toragee/EQToolTouch/EQTool/Battery.h

/*****************************************************************************
 *  Battery.h  -  ESP32-C6-Touch-LCD-1.47 배터리 전압 읽기
 *
 *  회로도 (BAT 블록):
 *      VBAT --[ R21 200K ]--+--[ R22 100K ]-- GND
 *                           |
 *                        BAT_ADC (GPIO0)
 *
 *  분압비 = (200K + 100K) / 100K = 3
 *  => VBAT = ADC 읽은 전압 x 3
 *
 *  1셀 LiPo 만충 4.2V -> ADC 에는 1.4V 가 걸리므로 C6 ADC 범위에 여유가 있다.
 *
 *  ※ USB 가 꽂혀 있으면 충전 IC(ETA6098)가 전압을 끌어올리기 때문에
 *    이 값은 "배터리 잔량" 이 아니라 "충전 전압" 이다. 잔량으로 쓰지 말 것.
 ****************************************************************************/
#pragma once

#include <Arduino.h>

#define BAT_ADC_PIN     0           /* 회로도 BAT_ADC */
#define BAT_DIV_RATIO   3.0f        /* (200K + 100K) / 100K */
#define BAT_OVERSAMPLE  16          /* 평균 횟수 (노이즈 억제) */

/*  실측 보정 계수.
 *  분압 저항 오차(±1% 급 두 개)와 ESP32-C6 ADC 캘리브레이션(±2~3%)이
 *  겹치면 몇 %씩 어긋난다. 보통 낮게 읽힌다.
 *
 *  구하는 법: USB 를 꽂아 만충시킨 뒤
 *      1) 멀티미터로 배터리 단자 전압을 잰다        (예: 4.21 V)
 *      2) 같은 시점의 [BAT] 로그 값을 본다           (예: 4012 mV)
 *      3) BAT_CAL = 실측 / 로그 = 4210 / 4012 = 1.049
 *
 *  1.0 이면 보정 없음. 2~3 점에서 같은 비율이 나오는지 확인하면 더 좋다. */
#define BAT_CAL         1.000f

/* 배터리 전압 (mV). 분압 보정까지 끝난 값. */
float Battery_ReadMv(void);

/* 전압 -> 잔량 % (0~100). 1셀 LiPo 방전 곡선 기준. */
uint8_t Battery_Percent(float mv);
