toragee/EQToolTouch/EQTool/Display_ST7789.h

/*****************************************************************************
 *  DEPRECATED - 이전 보드(ESP32-C6-LCD-1.47 / ST7789) 전용이었다.
 *
 *  ESP32-C6-Touch-LCD-1.47 은 컨트롤러가 JD9853 이라 Display_LCD.* 로 교체됐다.
 *  기존 #include "Display_ST7789.h" 가 깨지지 않도록 전달만 한다.
 *  새 코드에서는 "Display_LCD.h" 를 직접 포함할 것.
 ****************************************************************************/
#pragma once
#include "Display_LCD.h"
